bamapookie/analog-binary-infinity-mirror-clock/extras/mtk33x9.h

/*
Supported NMEA Sentences for the MTK33x9 GPS chip used in the Adafruit Ultimate GPS Breakout Board
http://www.adafruit.com/products/746
Most of the contents of this file were lifted from
https://github.com/adafruit/Adafruit_GPS/blob/master/Adafruit_GPS.h
and are Copyrighted by Adafruit Industries.  Their license and copyright are included here.
*/
#ifndef _MTK33X9_H
#define _MTK33X9_H

// different commands to set the update rate from once a second (1 Hz) to 10 times a second (10Hz)
#define PMTK_SET_NMEA_UPDATE_100_MILLIHERTZ "$PMTK220,10000*2F"  // Once every 10 seconds, 100 millihertz.
#define PMTK_SET_NMEA_UPDATE_200_MILLIHERTZ "$PMTK220,5000*1B"   // Once every 5 seconds, 200 millihertz.
#define PMTK_SET_NMEA_UPDATE_1HZ "$PMTK220,1000*1F"
#define PMTK_SET_NMEA_UPDATE_2HZ "$PMTK220,500*2B"
#define PMTK_SET_NMEA_UPDATE_5HZ "$PMTK220,200*2C"
#define PMTK_SET_NMEA_UPDATE_10HZ "$PMTK220,100*2F"
// Position fix update rate commands.
#define PMTK_API_SET_FIX_CTL_100_MILLIHERTZ "$PMTK300,10000,0,0,0,0*2C"  // Once every 10 seconds, 100 millihertz.
#define PMTK_API_SET_FIX_CTL_200_MILLIHERTZ "$PMTK300,5000,0,0,0,0*18"   // Once every 5 seconds, 200 millihertz.
#define PMTK_API_SET_FIX_CTL_1HZ "$PMTK300,1000,0,0,0,0*1C"
#define PMTK_API_SET_FIX_CTL_5HZ "$PMTK300,200,0,0,0,0*2F"
// Can't fix position faster than 5 times a second!

#define PMTK_SET_BAUD_115200 "$PMTK251,115200*1F"
#define PMTK_SET_BAUD_57600 "$PMTK251,57600*2C"
#define PMTK_SET_BAUD_57600 "$PMTK251,38400*27"
#define PMTK_SET_BAUD_19200 "$PMTK251,19200*22"
#define PMTK_SET_BAUD_14400 "$PMTK251,14400*29"
#define PMTK_SET_BAUD_9600 "$PMTK251,9600*17"
#define PMTK_SET_BAUD_4800 "$PMTK251,4800*14"

// turn on only the second sentence (GPRMC)
#define PMTK_SET_NMEA_OUTPUT_RMCONLY "$PMTK314,0,1,0,0,0,0,0,0,0,0,0,0,0,0,0,0,0,0,0*29"
// turn on GPRMC and GGA
#define PMTK_SET_NMEA_OUTPUT_RMCGGA "$PMTK314,0,1,0,1,0,0,0,0,0,0,0,0,0,0,0,0,0,0,0*28"
// turn on ALL THE DATA
#define PMTK_SET_NMEA_OUTPUT_ALLDATA "$PMTK314,1,1,1,1,1,1,0,0,0,0,0,0,0,0,0,0,0,0,0*28"
// turn on ALL ALL THE DATA
#define PMTK_SET_NMEA_OUTPUT_ALLDATAPLUS "$PMTK314,1,1,1,1,1,1,0,0,0,0,0,0,0,0,0,0,0,1,1*28"
// turn on ZDA output (Not officially supported, but works)
#define PMTK_SET_NMEA_OUTPUT_ZDA "$PMTK314,0,0,0,0,0,0,0,0,0,0,0,0,0,0,0,0,0,1,0*29"
// turn off output
#define PMTK_SET_NMEA_OUTPUT_OFF "$PMTK314,0,0,0,0,0,0,0,0,0,0,0,0,0,0,0,0,0,0,0*28"

// to generate your own sentences, check out the MTK command datasheet and use a checksum calculator
// such as the awesome http://www.hhhh.org/wiml/proj/nmeaxor.html

#define PMTK_LOCUS_STARTLOG "$PMTK185,0*22"
#define PMTK_LOCUS_STOPLOG "$PMTK185,1*23"
#define PMTK_LOCUS_STARTSTOPACK "$PMTK001,185,3*3C"
#define PMTK_LOCUS_QUERY_STATUS "$PMTK183*38"
#define PMTK_LOCUS_ERASE_FLASH "$PMTK184,1*22"
#define LOCUS_OVERLAP 0
#define LOCUS_FULLSTOP 1

#define PMTK_ENABLE_SBAS "$PMTK313,1*2E"
#define PMTK_ENABLE_WAAS "$PMTK301,2*2E"

// standby command & boot successful message
#define PMTK_STANDBY "$PMTK161,0*28"
#define PMTK_STANDBY_SUCCESS "$PMTK001,161,3*36"  // Not needed currently
#define PMTK_AWAKE "$PMTK010,002*2D"

// ask for the release and version
#define PMTK_Q_RELEASE "$PMTK605*31"

// request for updates on antenna status
#define PGCMD_ANTENNA "$PGCMD,33,1*6C"
#define PGCMD_NOANTENNA "$PGCMD,33,0*6D"

#endif
